probablyfine/IoTDnD/photos/IMG_6146.jpg

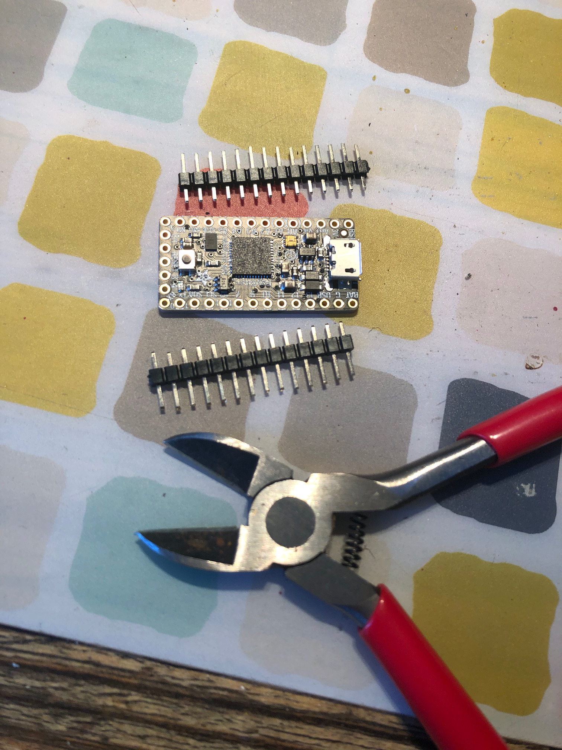
photos/IMG_6146.jpg
