probablyfine/IoTDnD/photos/IMG_6147.jpg

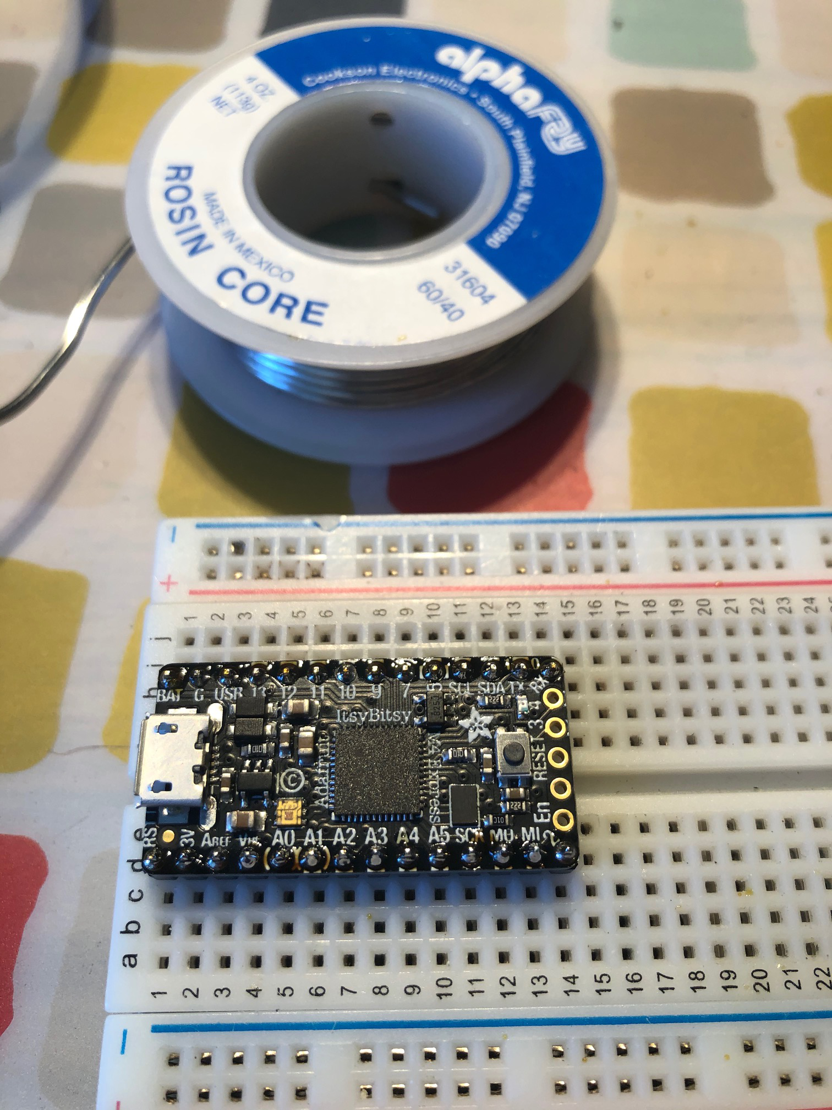
photos/IMG_6147.jpg
