probablyfine/IoTDnD/photos/IMG_6148.jpg

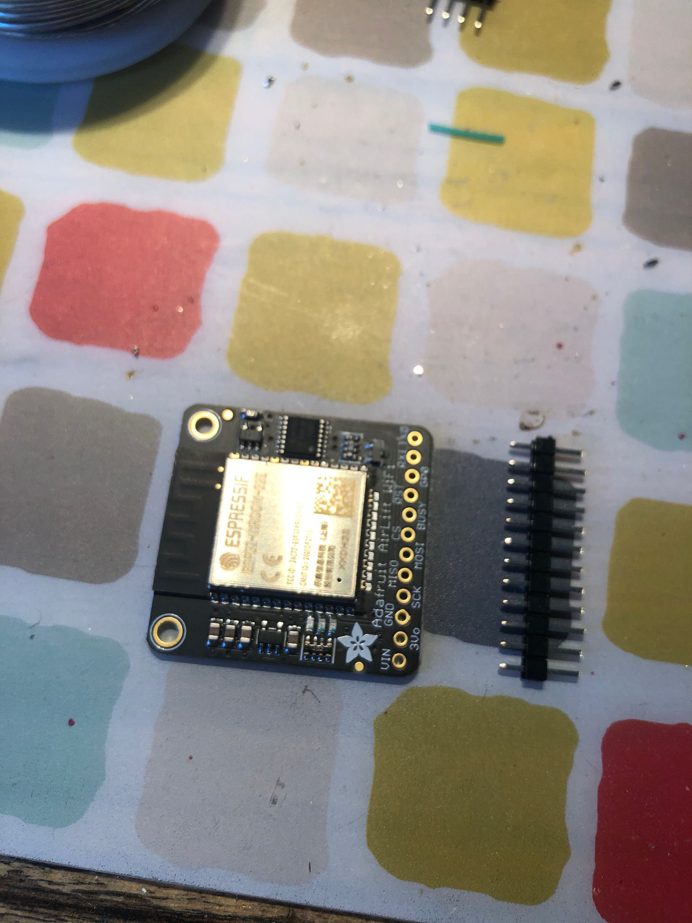
photos/IMG_6148.jpg
