probablyfine/IoTDnD/photos/IMG_6149.jpg

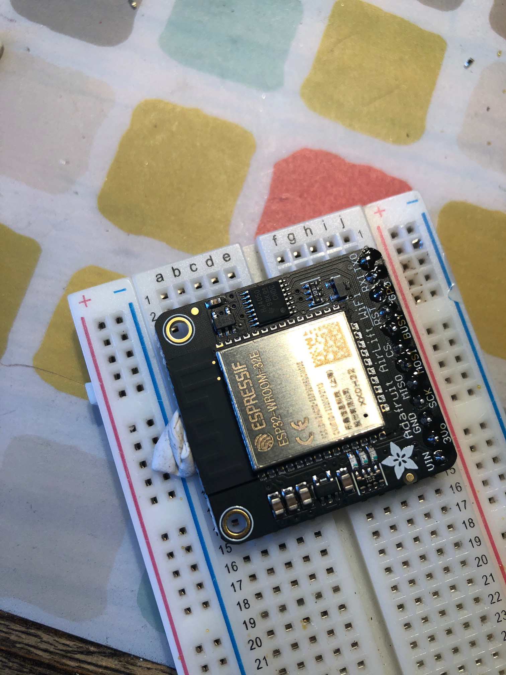
photos/IMG_6149.jpg
