probablyfine/IoTDnD/photos/IMG_6152.jpg

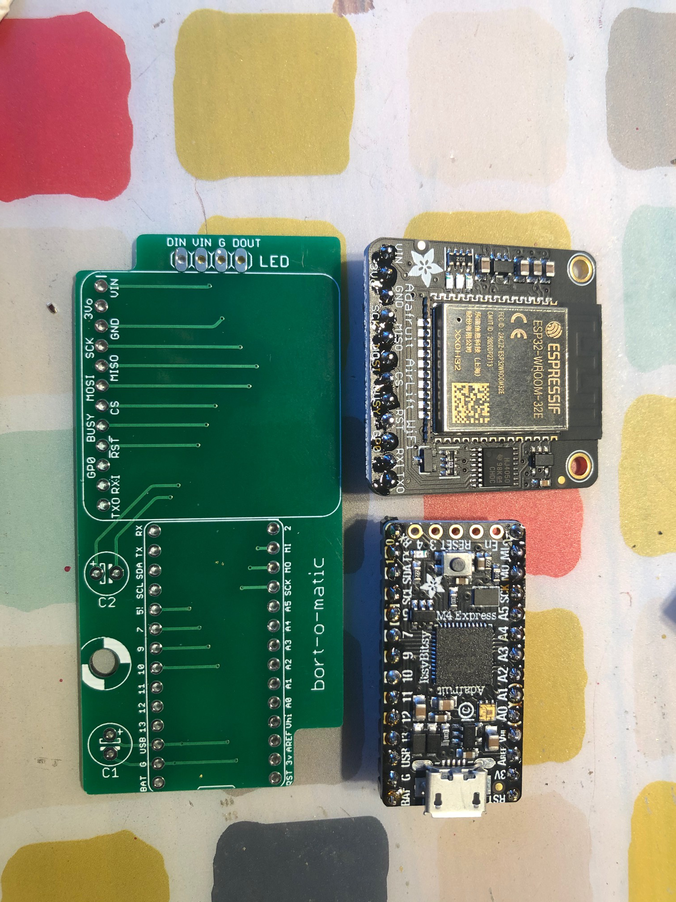
photos/IMG_6152.jpg
