probablyfine/IoTDnD/photos/IMG_6153.jpg

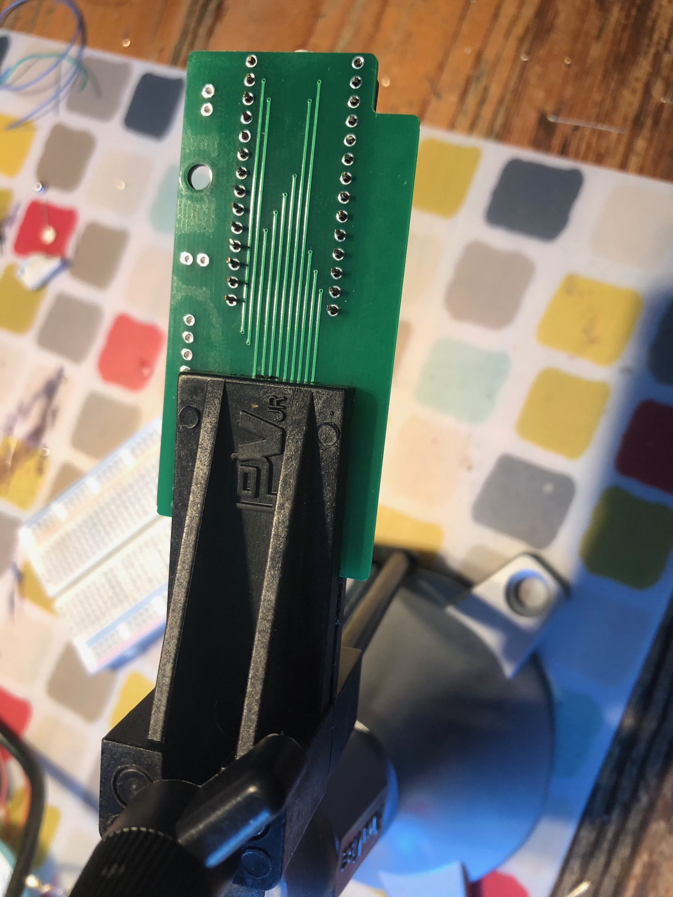
photos/IMG_6153.jpg
