probablyfine/IoTDnD/photos/IMG_6154.jpg

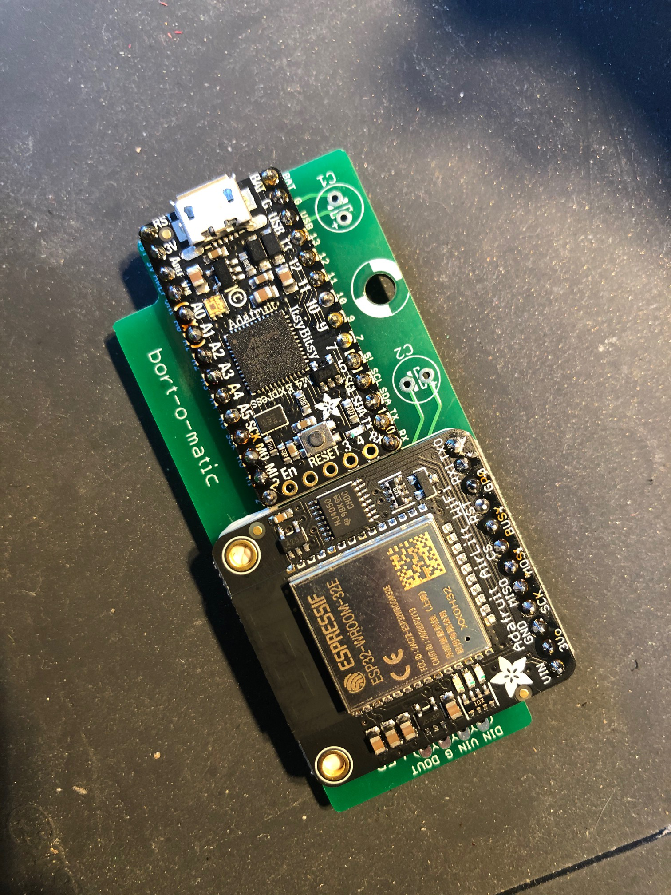
photos/IMG_6154.jpg
