probablyfine/IoTDnD/photos/IMG_6155.jpg

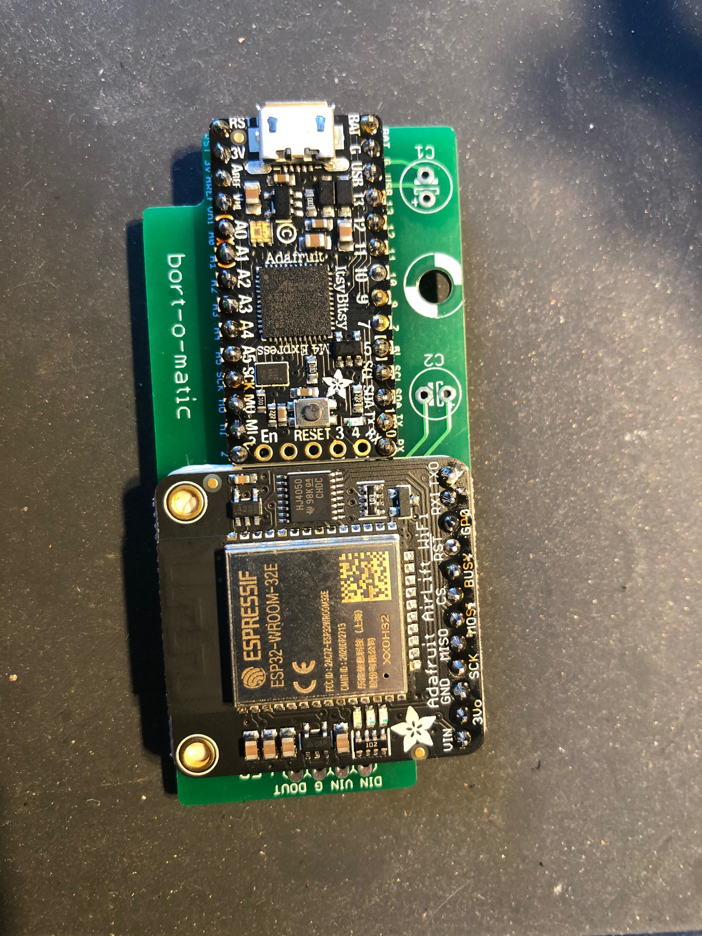
photos/IMG_6155.jpg
