probablyfine/IoTDnD/photos/IMG_6156.jpg

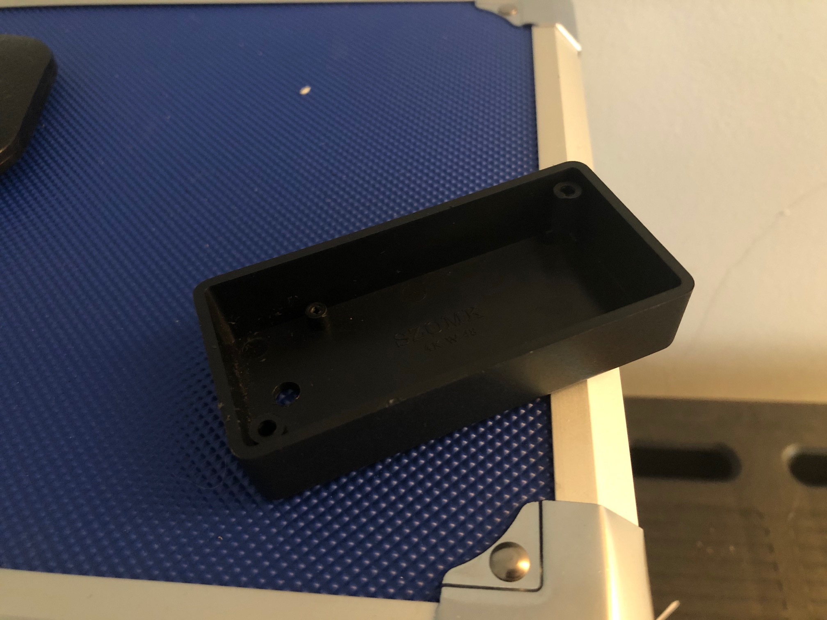
photos/IMG_6156.jpg
