probablyfine/IoTDnD/photos/IMG_6158.jpg

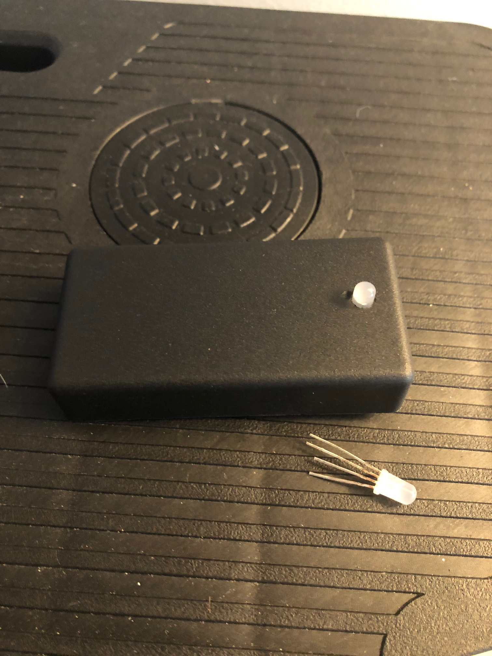
photos/IMG_6158.jpg
