probablyfine/IoTDnD/photos/IMG_6159.jpg

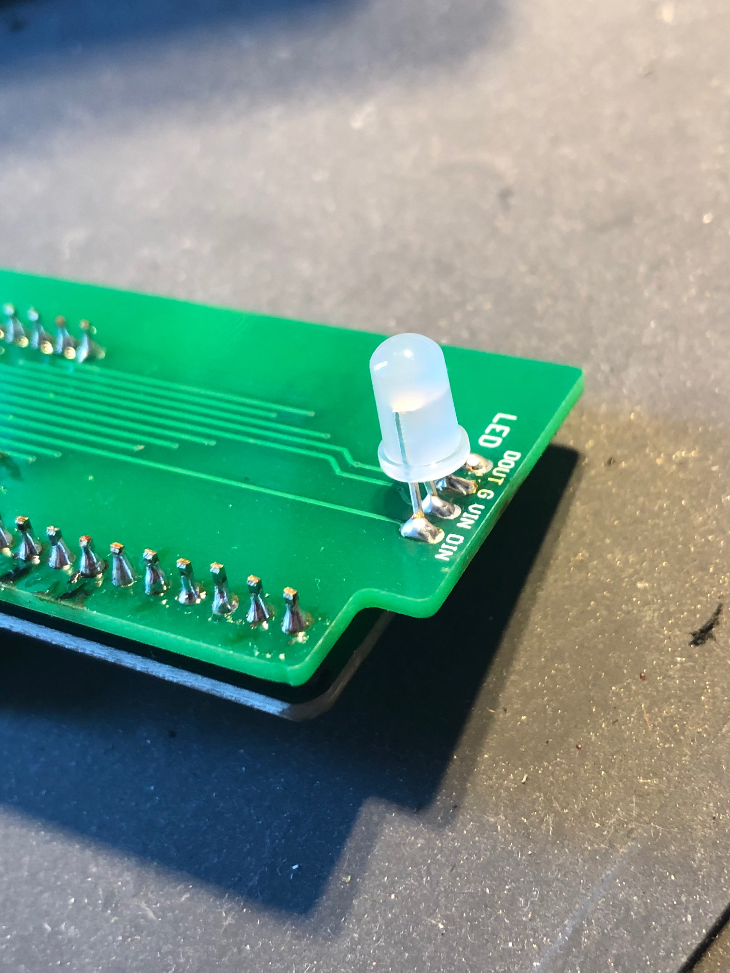
photos/IMG_6159.jpg
