probablyfine/IoTDnD/photos/IMG_6160.jpg

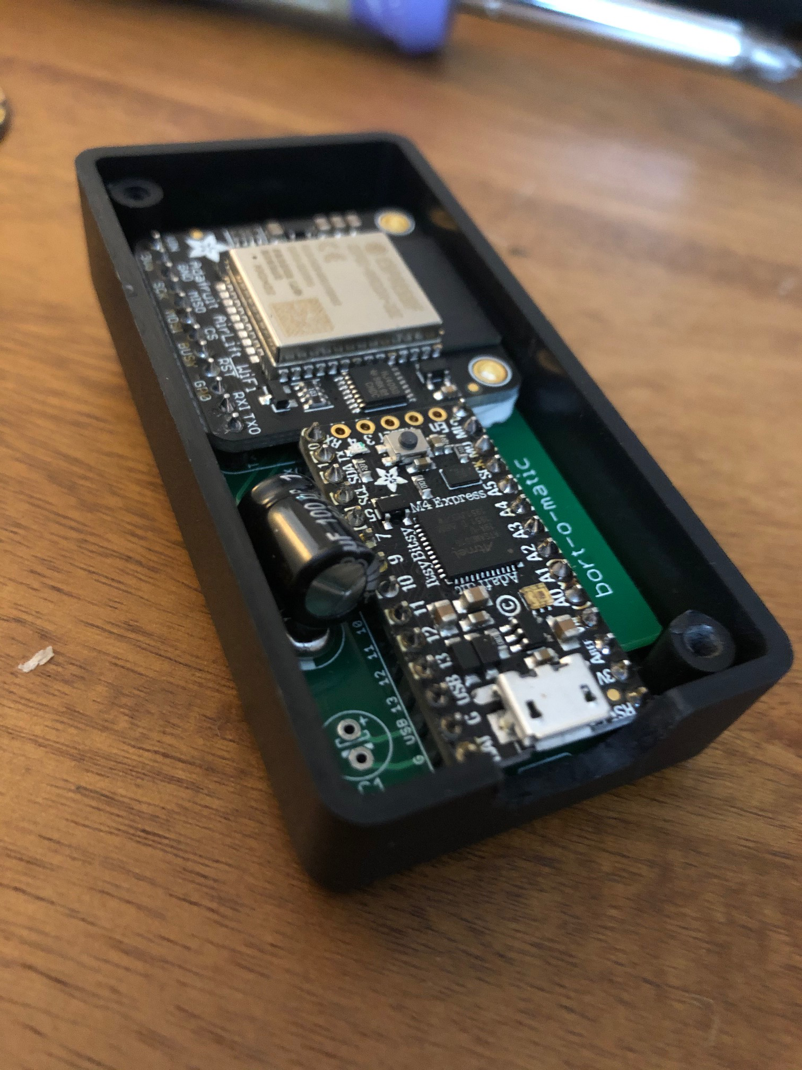
photos/IMG_6160.jpg
