probablyfine/IoTDnD/photos/IMG_6163.jpg

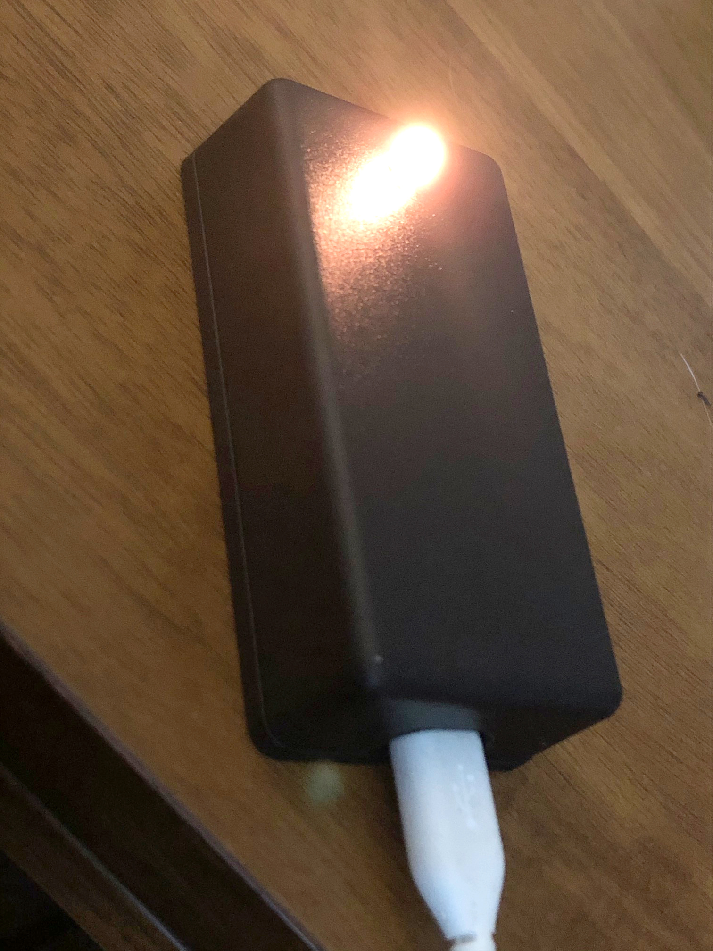
photos/IMG_6163.jpg
